UtolsoLoteriKutya/Power-management-with-alarm-for-Raspberry-Pi3B-/index_elemei/image003.jpg

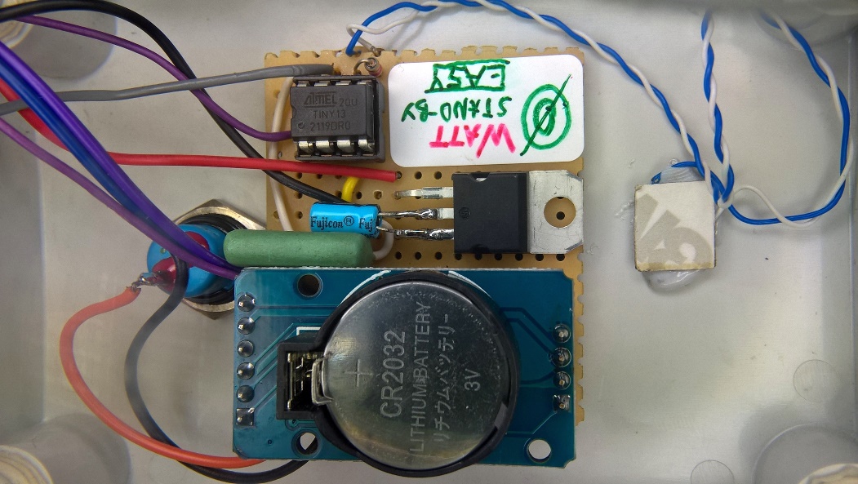
index_elemei/image003.jpg
